VoronMods/EuroProbe/STL/Omron90_M3 Tap(2.5).stl

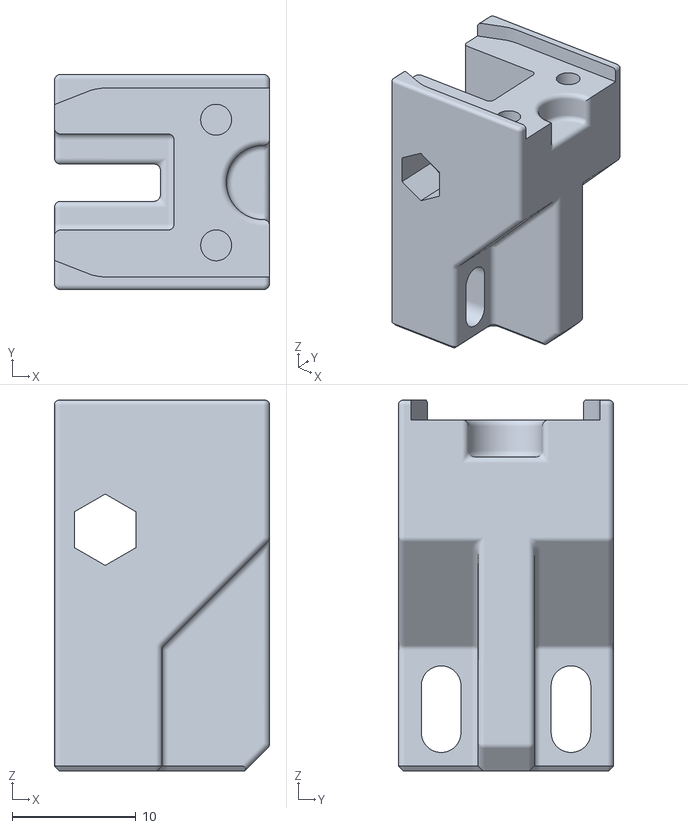
[picture p26: CAD file, 2022-01-17]
STL/Omron90_M3 Tap(2.5).stl
17.4 x 17.4 x 30.0
