VoronMods/EuroProbe/STL/VoronGantryMount2_mount.stl

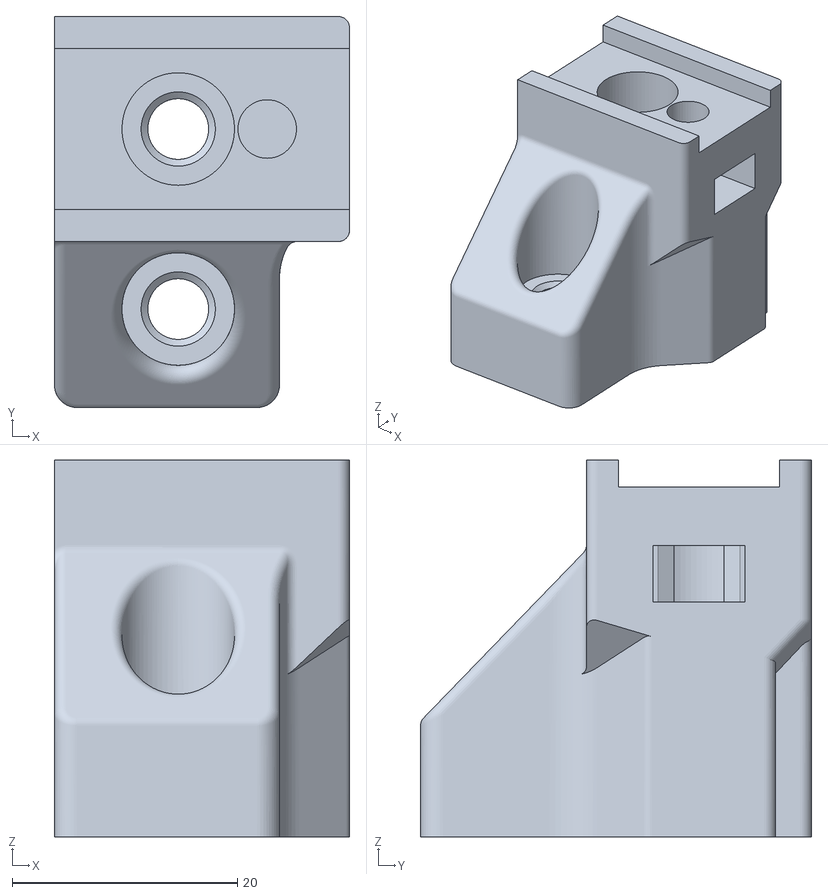
[picture p27: CAD file, 2022-01-17]
STL/VoronGantryMount2_mount.stl
26.2 x 34.8 x 33.5
