VoronMods/EuroProbe/STL/ProbeDock_for_Klicky_mount.stl

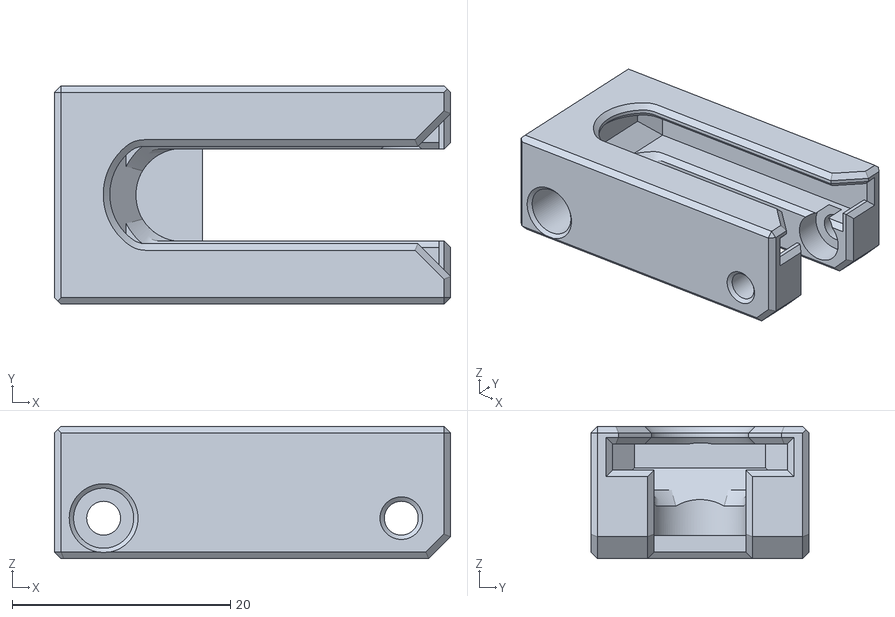
[picture p28: CAD file, 2022-01-17]
STL/ProbeDock_for_Klicky_mount.stl
36.3 x 20.0 x 12.1
