VoronMods/EuroProbe/STL/Voron2.4BedMount_Dock.stl

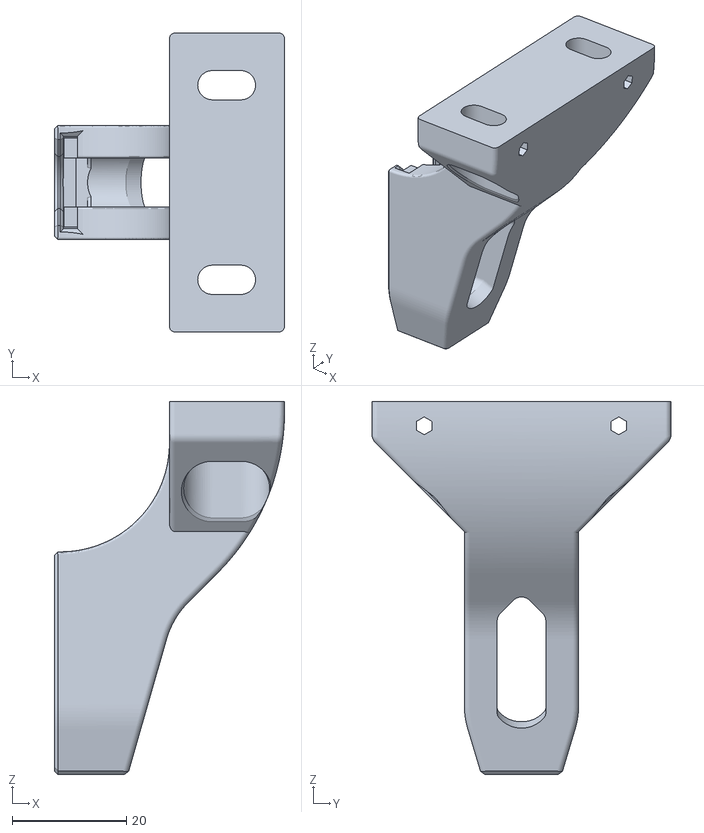
[picture p29: CAD file, 2022-01-17]
STL/Voron2.4BedMount_Dock.stl
40.2 x 52.2 x 65.2
