VoronMods/EuroProbe/STL/VoronGantryMount2_dock.stl

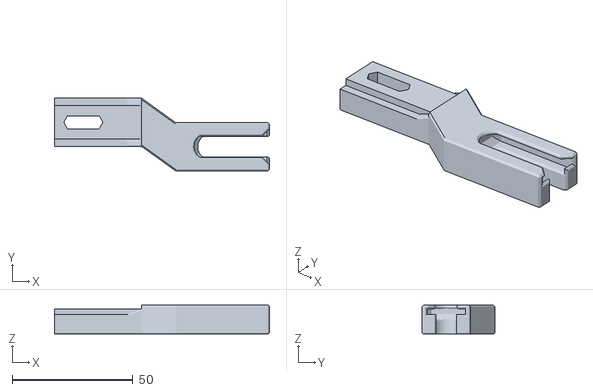
[picture p30: CAD file, 2022-01-17]
STL/VoronGantryMount2_dock.stl
89.0 x 30.1 x 12.0
